lambdakb/trackball-lt7dk/output/img/lt7dk-pcb-bottom.png

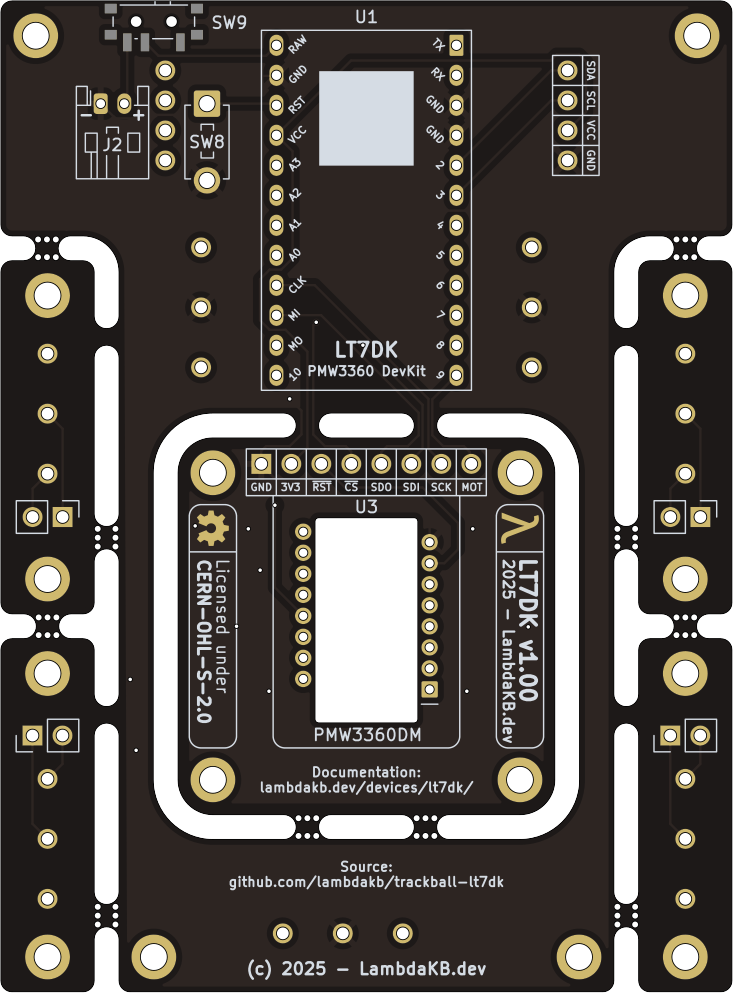
output/img/lt7dk-pcb-bottom.png
