lambdakb/trackball-lt7dk/output/img/lt7dk-pcb-top.png

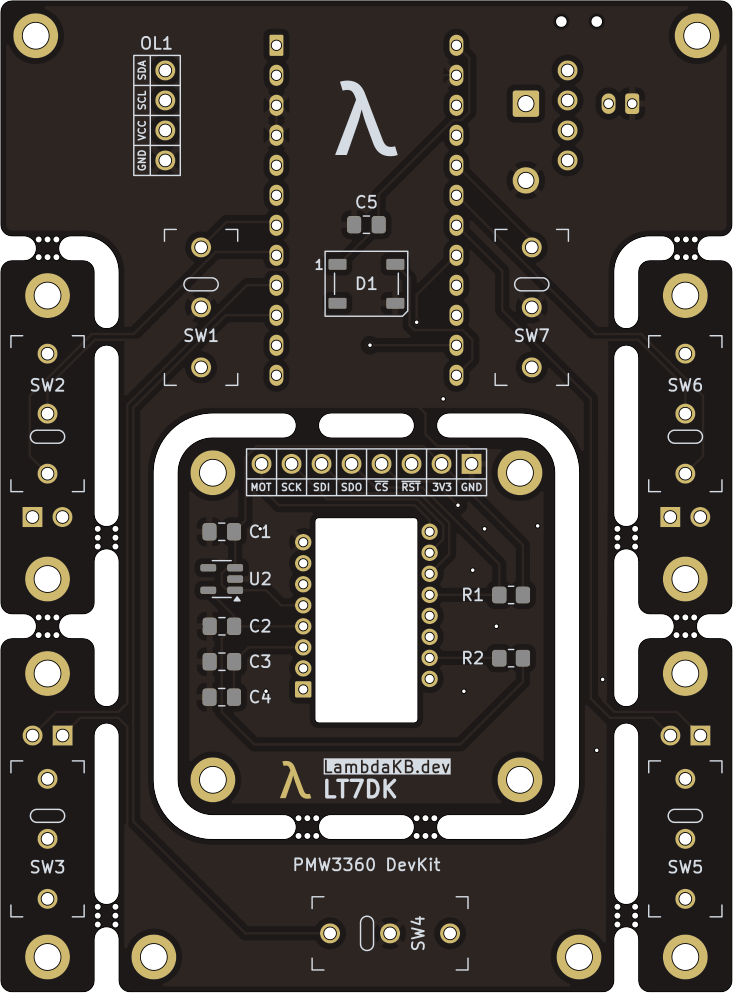
output/img/lt7dk-pcb-top.png
